elimbaum/backscatter-capstone/img/angle2.jpeg

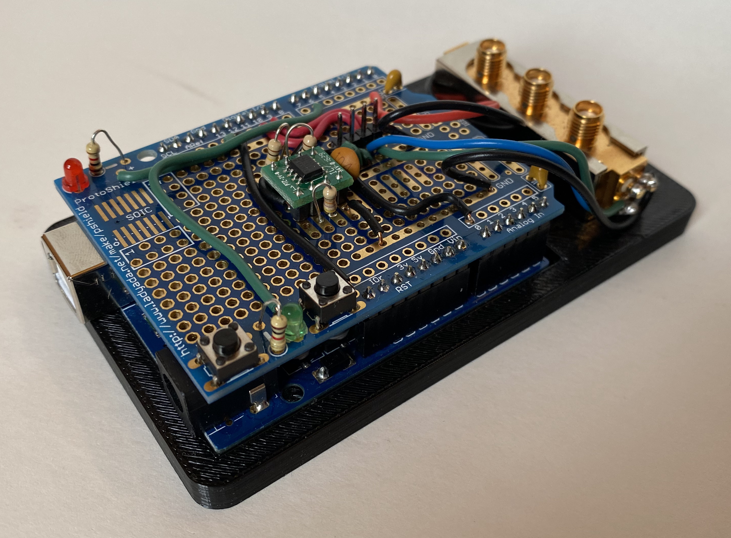
img/angle2.jpeg
