elimbaum/backscatter-capstone/arduino/test_8b10b/test_8b10b.ino

#include "8b10b.h"

char serial_buffer[256];

void setup() {
  // put your setup code here, to run once:
  Serial.begin(115200);

  for (int i = 0; i <= 0xFF; i++) {
    uint16_t e = encode_8b10b(CODE_DATA, i);
    Serial.print(i, BIN);
    sprintf(serial_buffer, "\t%3d -> %3d ~ ", i, e);
    Serial.print(serial_buffer);
    Serial.println(e, BIN);
  }

}

void loop() {

}
