elimbaum/backscatter-capstone/arduino/util/msg_queue.h

/* Message queue - header. */

#ifndef _MSG_QUEUE_H
#define _MSG_QUEUE_H

#include "fsk.h"
#include "Arduino.h"

// queue max size, bytes
#define QUEUE_SIZE 32
#define _QUEUE_SIZE_BITS (QUEUE_SIZE * 8L)

#define QUEUE_EMPTY -1

// Hamming(7, 4), so we're sending data bits slower than expected
// #define HAMMING_FACTOR (7.0 / 4)

// how long it would take to send the whole queue
// #define MS_TO_SEND_QUEUE (1000L * HAMMING_FACTOR * _QUEUE_SIZE_BITS / BITS_PER_SECOND)

#define MS_TO_SEND_QUEUE (1000L * _QUEUE_SIZE_BITS / FM0_BITS_PER_SECOND)

/* how much we would like to refill the queue (higher
 * fractions mean we wait longer to refill)
 */
#define QUEUE_REFILL_FRACTION   0.95
#define QUEUE_REFILL_MS  (MS_TO_SEND_QUEUE * QUEUE_REFILL_FRACTION)

int queue_empty_spots();
bool enqueue(uint8_t item);
int dequeue();
int queue_count();
void enqueue_block(uint8_t);

#endif
