elimbaum/backscatter-capstone/arduino/util/8b10b_tables.h

const uint8_t table_5b6b[][2] = {
  {0x27, 0x18},
  {0x1d, 0x22},
  {0x2d, 0x12},
  {0x31, 0x31},
  {0x35, 0x0a},
  {0x29, 0x29},
  {0x19, 0x19},
  {0x38, 0x07},
  {0x39, 0x06},
  {0x25, 0x25},
  {0x15, 0x15},
  {0x34, 0x34},
  {0x0d, 0x0d},
  {0x2c, 0x2c},
  {0x1c, 0x1c},
  {0x17, 0x28},
  {0x1b, 0x24},
  {0x23, 0x23},
  {0x13, 0x13},
  {0x32, 0x32},
  {0x0b, 0x0b},
  {0x2a, 0x2a},
  {0x1a, 0x1a},
  {0x3a, 0x05},
  {0x33, 0x0c},
  {0x26, 0x26},
  {0x16, 0x16},
  {0x36, 0x09},
  {0x0e, 0x0e},
  {0x2e, 0x11},
  {0x1e, 0x21},
  {0x2b, 0x14},
};

const uint8_t table_data_3b4b[][2] = {
  {0x0b, 0x04},
  {0x09, 0x09},
  {0x05, 0x05},
  {0x0c, 0x03},
  {0x0d, 0x02},
  {0x0a, 0x0a},
  {0x06, 0x06},
  {0x0e, 0x01},
  {0x07, 0x08},
};

const uint8_t table_control_3b4b[][2] = {
  {0x0b, 0x04},
  {0x06, 0x09},
  {0x0a, 0x05},
  {0x0c, 0x03},
  {0x0d, 0x02},
  {0x05, 0x0a},
  {0x09, 0x06},
  {0x07, 0x08},
};
